hallard/NodeMCU-Gateway/pictures/NodeMCU-Gateway-brd.png

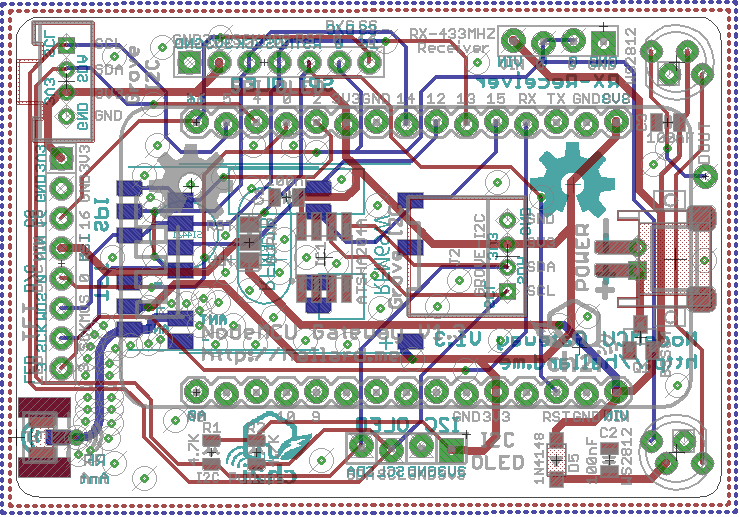
pictures/NodeMCU-Gateway-brd.png
